durgadas311/homebrew3/kicad/homebrew3.kicad_sch

## KiCad design kicad/homebrew3.kicad_sch (2022-12-18, an earlier design)

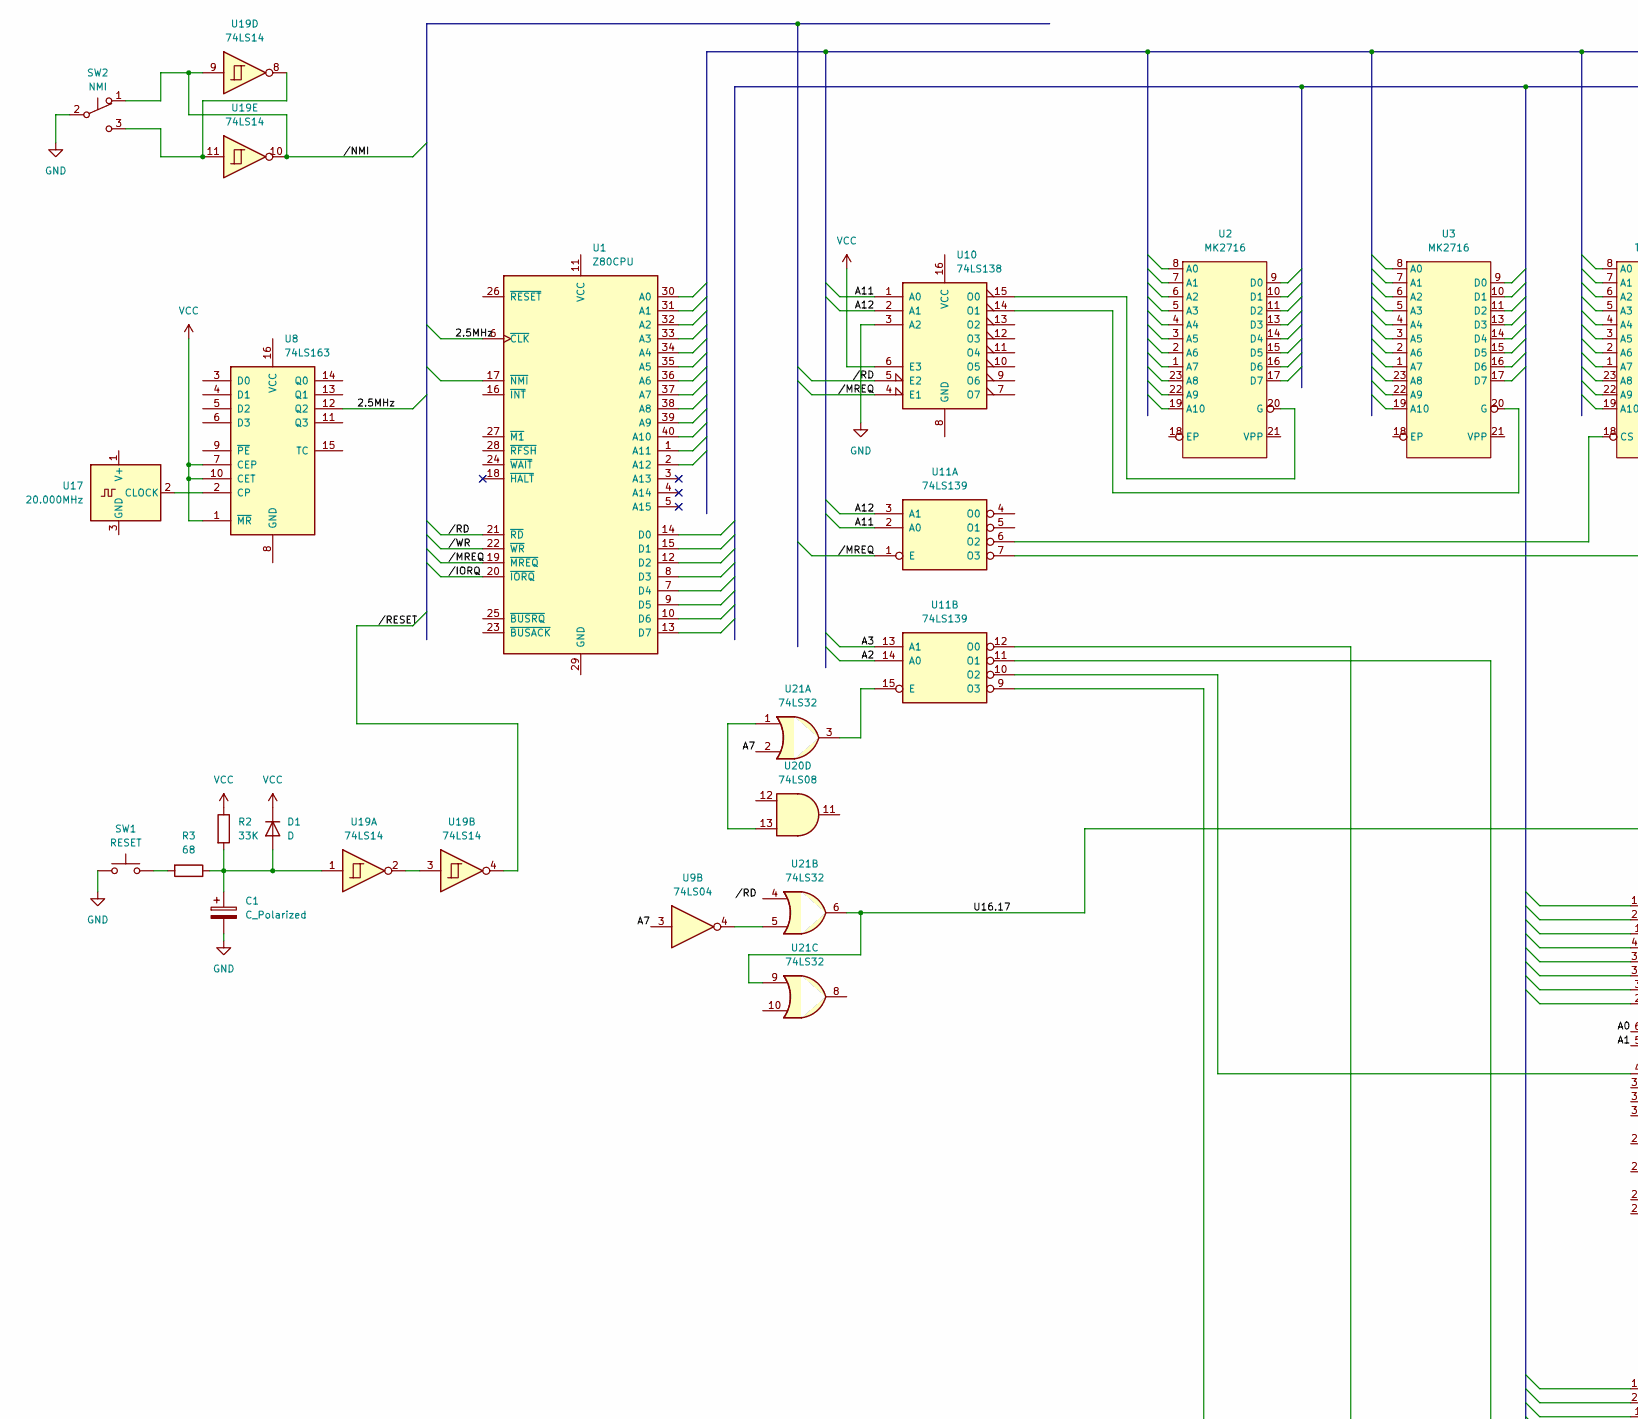
[picture p5: schematic homebrew3.kicad_sch, part in row 1, column 1]

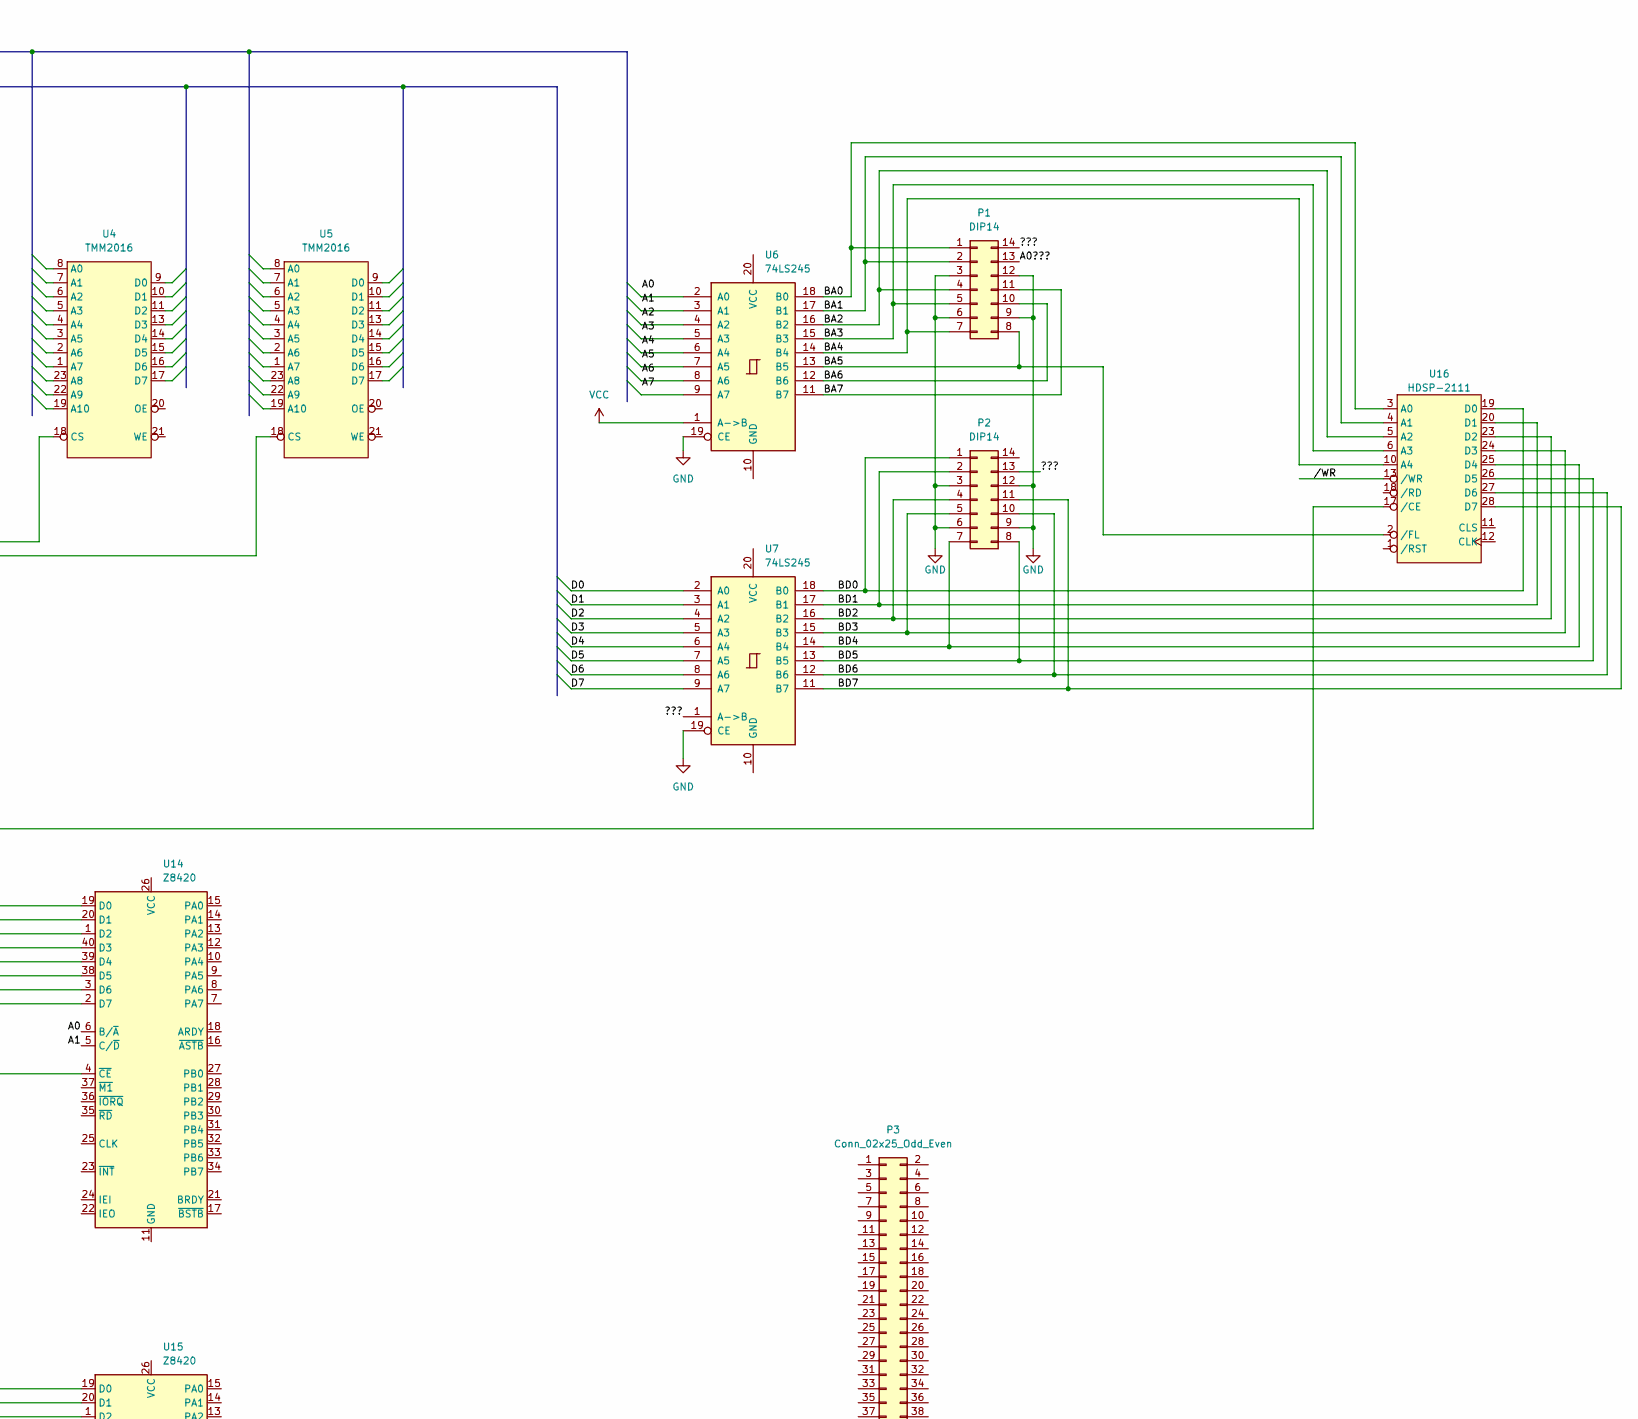
[picture p6: schematic homebrew3.kicad_sch, part in row 1, column 2]

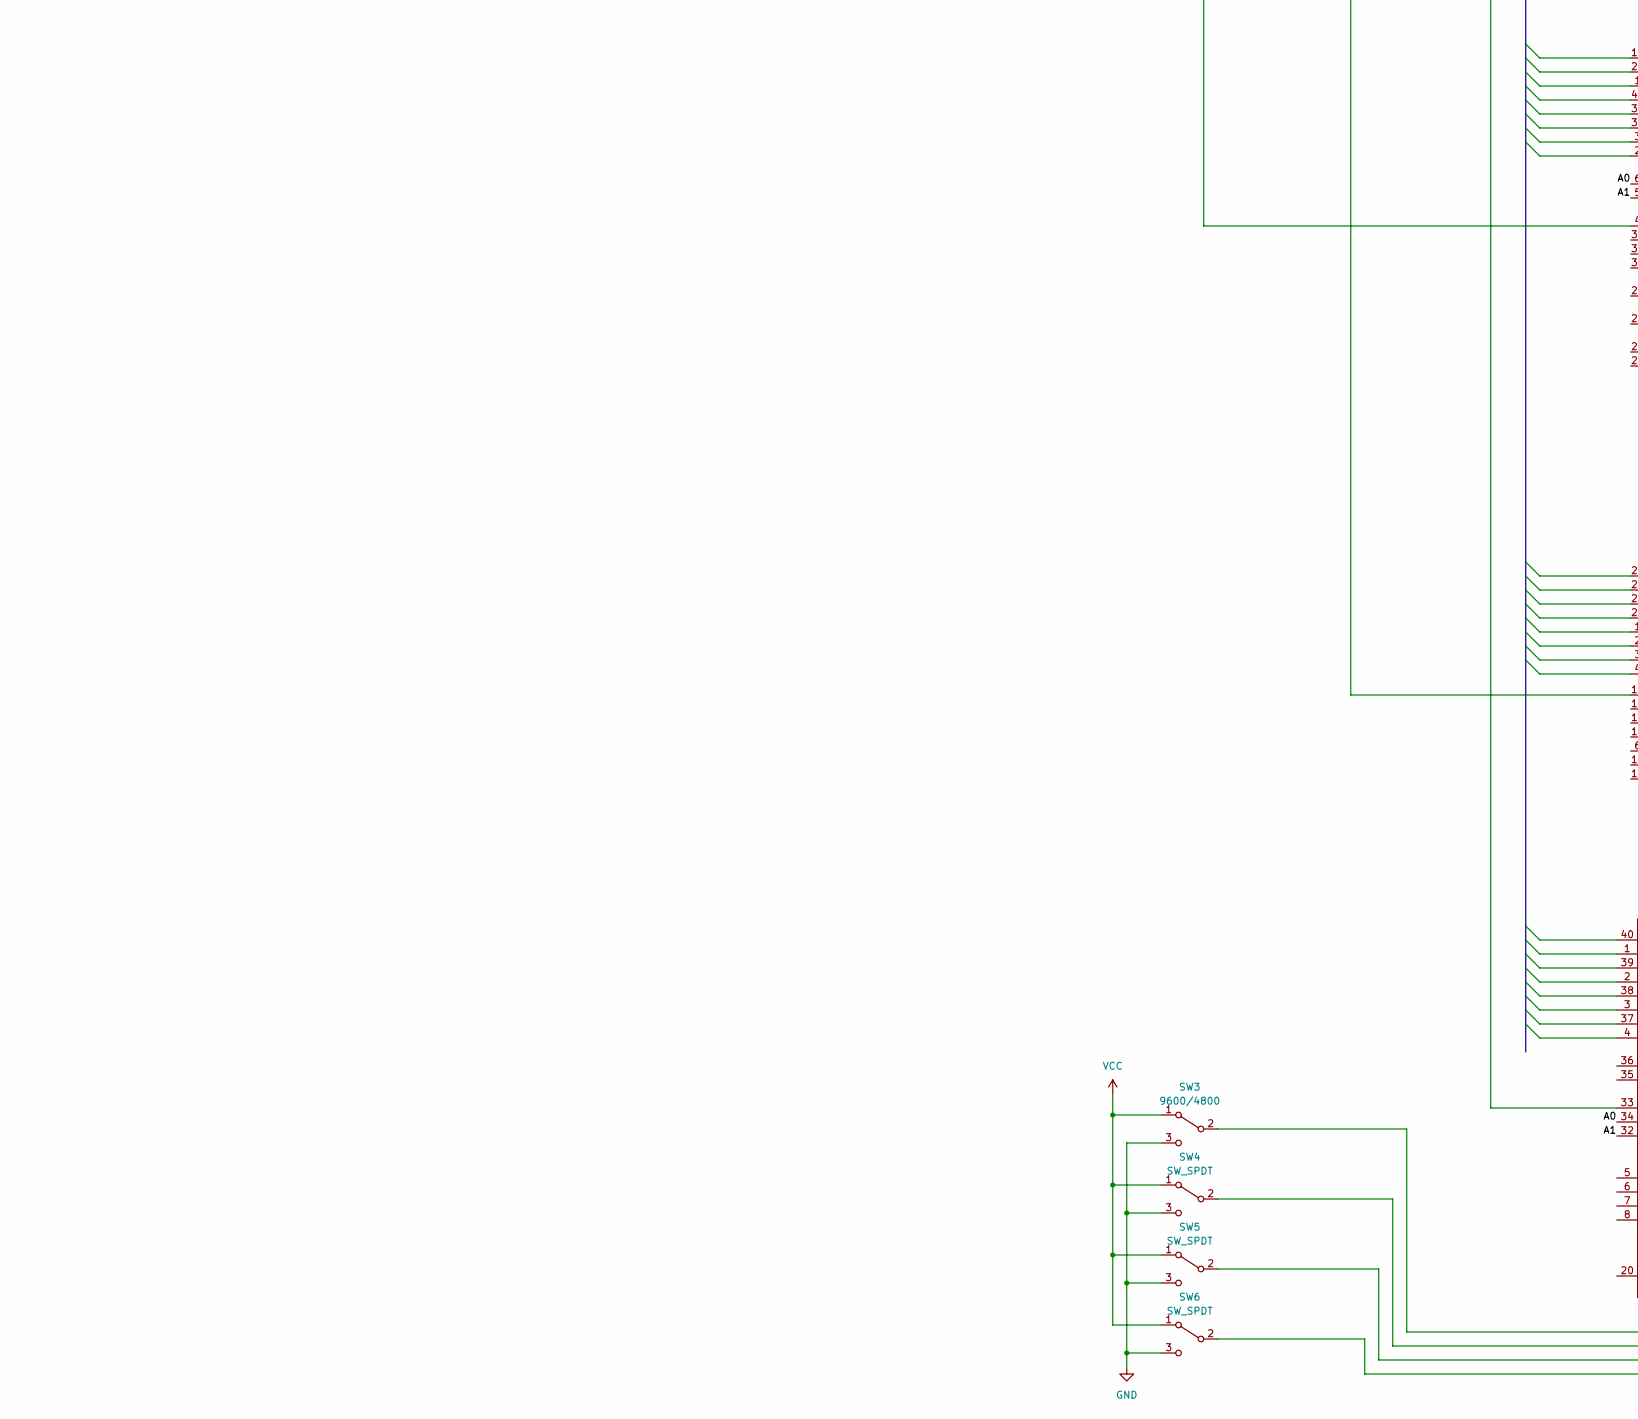
[picture p7: schematic homebrew3.kicad_sch, part in row 2, column 1]

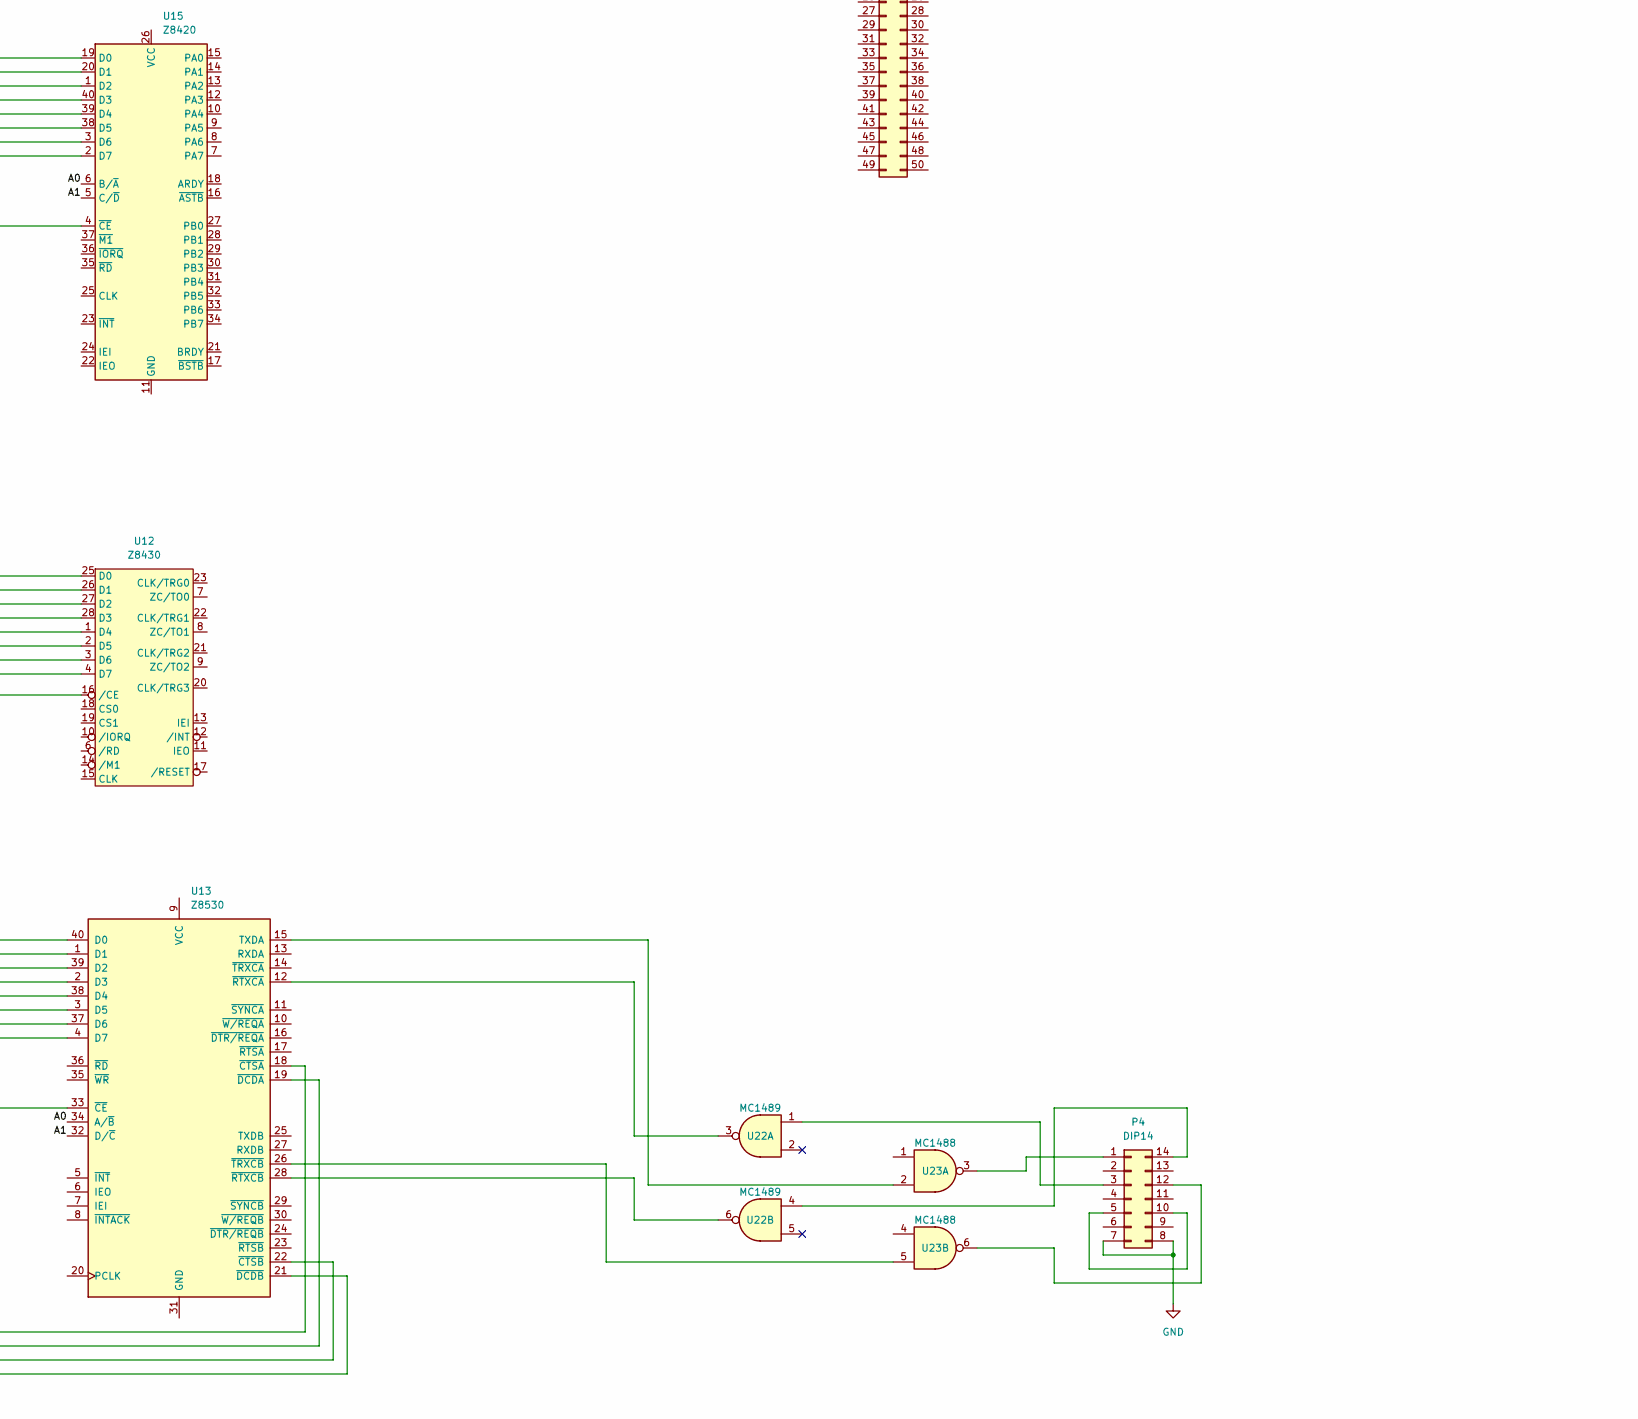
[picture p8: schematic homebrew3.kicad_sch, part in row 2, column 2]

Parts:
C1: C_Polarized
D1: D
P1, P2, P4: DIP14
P3: Conn_02x25_Odd_Even
R2: 33K
R3: 68
SW1: RESET
SW2: NMI
SW3: 9600/4800
SW4, SW5, SW6: SW_SPDT
U1: Z80CPU
U2, U3: MK2716
U4, U5: TMM2016
U6, U7: 74LS245
U8: 74LS163
U9: 74LS04
U10: 74LS138
U11: 74LS139
U12: Z8430
U13: Z8530
U14, U15: Z8420; DIP-40_W15.24mm
U16: HDSP-2111
U17: 20.000MHz; SOT-323_SC-70
U19: 74LS14
U20: 74LS08
U21: 74LS32
U22: MC1489
U23: MC1488

Connections:
2.5MHz: U1.6 (~CLK), U8.12 (Q2)
???: P1.14, P2.13, U7.1 (A->B)
A0: U13.34 (A/~B), U14.6 (B/~A), U15.6 (B/~A)
A0???: P1.13
A1: U13.32 (D/~C), U14.5 (C/~D), U15.5 (C/~D)
A2: U11.14 (A0)
A3: U11.13 (A1)
A7: U21.2
A11: U10.1 (A0), U11.2 (A0)
A12: U10.2 (A1), U11.3 (A1)
BA0: P1.1, U6.18 (B0), U16.3 (A0)
BA1: P1.2, U6.17 (B1), U16.4 (A1)
BA2: P1.4, U6.16 (B2), U16.5 (A2)
BA3: P1.5, U6.15 (B3), U16.6 (A3)
BA4: P1.7, U6.14 (B4), U16.10 (A4)
BA5: P1.8, U6.13 (B5), U16.2 (/FL)
BA6: P1.10, U6.12 (B6)
BA7: P1.11, U6.11 (B7)
BD0: P2.1, U7.18 (B0), U16.19 (D0)
BD1: P2.2, U7.17 (B1), U16.20 (D1)
BD2: P2.4, U7.16 (B2), U16.23 (D2)
BD3: P2.5, U7.15 (B3), U16.24 (D3)
BD4: P2.7, U7.14 (B4), U16.25 (D4)
BD5: P2.8, U7.13 (B5), U16.26 (D5)
BD6: P2.10, U7.12 (B6), U16.27 (D6)
BD7: P2.11, U7.11 (B7), U16.28 (D7)
D0: U7.2 (A0)
D1: U7.3 (A1)
D2: U7.4 (A2)
D3: U7.5 (A3)
D4: U7.6 (A4)
D5: U7.7 (A5)
D6: U7.8 (A6)
D7: U7.9 (A7)
unnamed: C1.1, D1.2 (A), R2.2, R3.1, U19.1
unnamed: P1.3, P1.6, P2.3, P2.6
unnamed: P1.9, P1.12, P2.9, P2.12
unnamed: P4.1, U23.3
unnamed: P4.3, U22.1
unnamed: P4.7, P4.8
unnamed: P4.5, P4.10
unnamed: P4.12, U23.6
unnamed: P4.14, U22.4
unnamed: R3.2, SW1.2
unnamed: SW2.3 (C), U19.8, U19.11
unnamed: SW3.1 (A), SW4.1 (A), SW5.1 (A), SW6.1 (A)
unnamed: SW3.2 (B), U13.18 (~CTSA)
unnamed: SW3.3 (C), SW4.3 (C), SW5.3 (C), SW6.3 (C)
unnamed: SW4.2 (B), U13.19 (~DCDA)
unnamed: SW5.2 (B), U13.22 (~CTSB)
unnamed: SW6.2 (B), U13.21 (~DCDB)
unnamed: U8.1 (~MR), U8.7 (CEP), U8.10 (CET)
unnamed: U3.20 (G), U10.14 (O1)
unnamed: U2.20 (G), U10.15 (O0)
unnamed: U4.18 (CS), U11.6 (O2)
unnamed: U5.18 (CS), U11.7 (O3)
unnamed: U11.9 (O3), U15.4 (~CE)
unnamed: U11.10 (O2), U14.4 (~CE)
unnamed: U11.11 (O1), U13.33 (~CE)
unnamed: U11.12 (O0), U12.16 (/CE)
unnamed: U11.15 (E), U21.3
unnamed: U13.12 (~RTXCA), U22.3
unnamed: U13.15 (TXDA), U23.2
unnamed: U13.26 (~TRXCB), U23.5
unnamed: U13.28 (~RTXCB), U22.6
unnamed: U8.2 (CP), U17.2 (CLOCK)
unnamed: U19.2, U19.3
unnamed: U20.13, U21.1
unnamed: U9.4, U21.5
U16.17: U16.17 (/CE), U21.6, U21.9
/IORQ: U1.20 (~IORQ)
/MREQ: U1.19 (~MREQ), U10.4 (E1), U11.1 (E)
/NMI: SW2.1 (A), U19.9, U19.10
/RD: U1.21 (~RD), U10.5 (E2)
/RESET: U19.4
/WR: U1.22 (~WR), U16.13 (/WR)
